McCleanResearch/Optogenetic-Chemostat-Files/Microcontroller_Code/add_these_to_library/Intensity/Intensity.cpp

/*
  Intensity.cpp - Library for turning on 0-64 LEDs on 8x8 array.
  Created by Cameron J. Stewart, November 25, 2015.
  Released into the public domain.
*/

#include "Arduino.h"
#include "Intensity.h"
  // define max7219 _registers
#define  MAX7219_REG_NOOP     0x00
#define  MAX7219_REG_DIGIT0   0x01
#define  MAX7219_REG_DIGIT1   0x02
#define  MAX7219_REG_DIGIT2   0x03
#define  MAX7219_REG_DIGIT3   0x04
#define  MAX7219_REG_DIGIT4   0x05
#define  MAX7219_REG_DIGIT5   0x06
#define  MAX7219_REG_DIGIT6   0x07
#define  MAX7219_REG_DIGIT7   0x08
#define  MAX7219_REG_DECODEMODE 0x09
#define  MAX7219_REG_INTENSITY 0x0a
#define  MAX7219_REG_SCANLIMIT 0x0b
#define  MAX7219_REG_SHUTDOWN 0x0c
#define  MAX7219_REG_DISPLAYTEST 0x0f

Intensity::Intensity(int dataIn, int load, int clock){
	_dataIn=dataIn;
	_load=load;
	_clock=clock;
  
  int maxInUse=1;        // code only made to handle 1 LED Array
  int e = 0;           // just a variable
  

    pinMode(_dataIn, OUTPUT);
    pinMode(_clock,  OUTPUT);
    pinMode(_load,   OUTPUT);
  

  //initiation of the max 7219
    maxSingle(MAX7219_REG_SCANLIMIT, 0x07);      
    maxSingle(MAX7219_REG_DECODEMODE, 0x00);  // using an led matrix (not digits)
    maxSingle(MAX7219_REG_SHUTDOWN, 0x01);    // not in shutdown mode
    maxSingle(MAX7219_REG_DISPLAYTEST, 0x00); // no display test
    numLEDs(0);
    maxSingle(MAX7219_REG_INTENSITY, 0x0f);    // the first 0x0f is the value you can set
                                                    // range: 0x00 to 0x0f

}
void Intensity::PWM(byte _pwm){
  maxSingle(MAX7219_REG_INTENSITY, _pwm);    // the first 0x0f is the value you can set
                                            // range: 0x00 to 0x0f
}
void Intensity::numLEDs(int i){
  if(i==0){
      maxSingle(MAX7219_REG_DIGIT0,0);       //  - - - - - - - -
      maxSingle(MAX7219_REG_DIGIT1,0);       //  - - - - - - - -
      maxSingle(MAX7219_REG_DIGIT2,0);       //  - - - - - - - -
      maxSingle(MAX7219_REG_DIGIT3,0);       //  - - - - - - - -
      maxSingle(MAX7219_REG_DIGIT4,0);       //  - - - - - - - -
      maxSingle(MAX7219_REG_DIGIT5,0);       //  - - - - - - - -
      maxSingle(MAX7219_REG_DIGIT6,0);       //  - - - - - - - -
      maxSingle(MAX7219_REG_DIGIT7,0);       //  - - - - - - - -
  } else if(i==1){
      maxSingle(MAX7219_REG_DIGIT0,0);       //  - - - - - - - -
      maxSingle(MAX7219_REG_DIGIT1,0);       //  - - - - - - - -
      maxSingle(MAX7219_REG_DIGIT2,0);       //  - - - - - - - -
      maxSingle(MAX7219_REG_DIGIT3,0);       //  - - - - - - - -
      maxSingle(MAX7219_REG_DIGIT4,16);      //  - - - - + - - -
      maxSingle(MAX7219_REG_DIGIT5,0);       //  - - - - - - - -
      maxSingle(MAX7219_REG_DIGIT6,0);       //  - - - - - - - -
      maxSingle(MAX7219_REG_DIGIT7,0);       //  - - - - - - - -
  } else if(i==2){
      maxSingle(MAX7219_REG_DIGIT0,0);       //  - - - - - - - -
      maxSingle(MAX7219_REG_DIGIT1,0);       //  - - - - - - - -
      maxSingle(MAX7219_REG_DIGIT2,0);       //  - - - - - - - -
      maxSingle(MAX7219_REG_DIGIT3,8);       //  - - - + - - - -
      maxSingle(MAX7219_REG_DIGIT4,16);      //  - - - - + - - -
      maxSingle(MAX7219_REG_DIGIT5,0);       //  - - - - - - - -
      maxSingle(MAX7219_REG_DIGIT6,0);       //  - - - - - - - -
      maxSingle(MAX7219_REG_DIGIT7,0);       //  - - - - - - - -
  }else if(i==3){
      maxSingle(MAX7219_REG_DIGIT0,0);       //  - - - - - - - -
      maxSingle(MAX7219_REG_DIGIT1,0);       //  - - - - - - - -
      maxSingle(MAX7219_REG_DIGIT2,0);       //  - - - - - - - -
      maxSingle(MAX7219_REG_DIGIT3,24);      //  - - - + + - - -
      maxSingle(MAX7219_REG_DIGIT4,16);      //  - - - - + - - -
      maxSingle(MAX7219_REG_DIGIT5,0);       //  - - - - - - - -
      maxSingle(MAX7219_REG_DIGIT6,0);       //  - - - - - - - -
      maxSingle(MAX7219_REG_DIGIT7,0);       //  - - - - - - - -
  }else if(i==4){
      maxSingle(MAX7219_REG_DIGIT0,0);       //  - - - - - - - -
      maxSingle(MAX7219_REG_DIGIT1,0);       //  - - - - - - - -
      maxSingle(MAX7219_REG_DIGIT2,0);       //  - - - - - - - -
      maxSingle(MAX7219_REG_DIGIT3,24);      //  - - - + + - - -
      maxSingle(MAX7219_REG_DIGIT4,24);      //  - - - + + - - -
      maxSingle(MAX7219_REG_DIGIT5,0);       //  - - - - - - - -
      maxSingle(MAX7219_REG_DIGIT6,0);       //  - - - - - - - -
      maxSingle(MAX7219_REG_DIGIT7,0);       //  - - - - - - - -
  }else if(i==5){
      maxSingle(MAX7219_REG_DIGIT0,0);       //  - - - - - - - -
      maxSingle(MAX7219_REG_DIGIT1,0);       //  - - - - - - - -
      maxSingle(MAX7219_REG_DIGIT2,0);       //  - - - - - - - -
      maxSingle(MAX7219_REG_DIGIT3,24);      //  - - - + + - - -
      maxSingle(MAX7219_REG_DIGIT4,24);      //  - - - + + - - -
      maxSingle(MAX7219_REG_DIGIT5,32);      //  - - - - - + - -
      maxSingle(MAX7219_REG_DIGIT6,0);       //  - - - - - - - -
      maxSingle(MAX7219_REG_DIGIT7,0);       //  - - - - - - - -
  }else if(i==6){
      maxSingle(MAX7219_REG_DIGIT0,0);       //  - - - - - - - -
      maxSingle(MAX7219_REG_DIGIT1,0);       //  - - - - - - - -
      maxSingle(MAX7219_REG_DIGIT2,4);       //  - - + - - - - -
      maxSingle(MAX7219_REG_DIGIT3,24);      //  - - - + + - - -
      maxSingle(MAX7219_REG_DIGIT4,24);      //  - - - + + - - -
      maxSingle(MAX7219_REG_DIGIT5,32);      //  - - - - - + - -
      maxSingle(MAX7219_REG_DIGIT6,0);       //  - - - - - - - -
      maxSingle(MAX7219_REG_DIGIT7,0);       //  - - - - - - - -
  }else if(i==7){
      maxSingle(MAX7219_REG_DIGIT0,0);       //  - - - - - - - -
      maxSingle(MAX7219_REG_DIGIT1,0);       //  - - - - - - - -
      maxSingle(MAX7219_REG_DIGIT2,36);      //  - - + - - + - -
      maxSingle(MAX7219_REG_DIGIT3,24);      //  - - - + + - - -
      maxSingle(MAX7219_REG_DIGIT4,24);      //  - - - + + - - -
      maxSingle(MAX7219_REG_DIGIT5,32);      //  - - - - - + - -
      maxSingle(MAX7219_REG_DIGIT6,0);       //  - - - - - - - -
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
  while(i > 0) {
    mask = 0x01 << (i - 1);      // get bitmask
    digitalWrite( _clock, LOW);   // tick
    if (data & mask){            // choose bit
    	digitalWrite(_dataIn, HIGH);// send 1
	}else{
      digitalWrite(_dataIn, LOW); // send 0
    }
    digitalWrite(_clock, HIGH);   // tock
    --i;                         // move to lesser bit
  }
}

void Intensity::maxSingle( byte _reg, byte _col) {    
//maxSingle is the "easy"  function to use for a single max7219
  digitalWrite(_load, LOW);       // begin     
  putByte(_reg);                  // specify _register
  putByte(_col);//((data & 0x01) * 256) + data >> 1); // put data   
  digitalWrite(_load, LOW);       // and _load da stuff
  digitalWrite(_load,HIGH); 
}
